ENAC-Robotique/fabs_motor_board/firmware/src/OdometryDiff.cpp

#include "OdometryDiff.h"
#include "math.h"
#include "encoders.h"

extern "C" {
#include "printf.h"
#include "globalVar.h"
#include "stdutil.h"
}
#include "utils.h"
#include "communication.h"
#include "BytesWriteBuffer.h"
#include "messages.h"

using namespace protoduck;


void OdometryDiff::set_pos(double x, double y, double theta) {
  _x = x;
  _y = y;
  _theta = theta;
}

void OdometryDiff::init() {
  initEnc1(true);
  initEnc2(false);
  initEnc3(false);
  initEnc4(true);

  auto cb_recalage = [this](Message& msg) {
      if(msg.has_pos() && msg.msg_type() == Message::MsgType::COMMAND) {
        double x = msg.pos().get_x();
        double y = msg.pos().get_y();
        double theta = msg.pos().get_theta();
        set_pos(x, y, theta);
    }
  };
  register_callback(cb_recalage);
}

void OdometryDiff::update_pos(double elapsed) {
    static systime_t lastOdomReportTime = 0;
    int32_t delta_left = get_delta_enc3();
    int32_t delta_right = get_delta_enc4();

    double length = ((double)(delta_left + delta_right)/2.0)/CODING_INC_PER_MM;
    double angle = ((double)(delta_right - delta_left)/CODING_INC_PER_MM)/CODING_WHEELBASE;

    speed = length / elapsed;
    omega = angle / elapsed;
    _x = _x + length*cos(_theta + angle/2.0);
    _y = _y + length*sin(_theta + angle/2.0);
    _theta = center_radians(_theta + angle);


    if(chVTTimeElapsedSinceX(lastOdomReportTime) > chTimeMS2I(PERIOD_ODOM_REPORT)) {
      sendOdomReport();
      lastOdomReportTime = chVTGetSystemTime();
    }
}

void OdometryDiff::update_mot(double elapsed) {
  static systime_t lastSlipReportTime = 0;
  int32_t delta_mot_left = get_delta_enc1();
  int32_t delta_mot_right = get_delta_enc2();

  speed_left  = static_cast<double>(delta_mot_left) / (MOTOR_INC_PER_MM*elapsed);
  speed_right = static_cast<double>(delta_mot_right)/ (MOTOR_INC_PER_MM*elapsed);

  double th_left = speed - omega * WHEELBASE / 2.0;
  double th_right = speed + omega * WHEELBASE / 2.0;
  double sl = th_left - speed_left;
  double sr = th_right - speed_right;
  double alpha = 0.1;
  slip_left  = (1-alpha) * slip_left  + alpha * sl;
  slip_right = (1-alpha) * slip_right + alpha * sr;

  if(chVTTimeElapsedSinceX(lastSlipReportTime) > chTimeMS2I(PERIOD_SLIP_REPORT)) {
    if(abs(slip_left) > SLIP_THRESHOLD || abs(slip_right) > SLIP_THRESHOLD) {
      Message msg;
      auto& slip_report = msg.mutable_slip();
      slip_report.set_slip_left(slip_left);
      slip_report.set_slip_right(slip_right);
      post_message(msg, Message::MsgType::STATUS, TIME_IMMEDIATE);
      lastSlipReportTime = chVTGetSystemTime();
    }
  }
}


msg_t OdometryDiff::sendOdomReport() {
  Message msg;
  auto& pos_report = msg.mutable_pos();
  pos_report.set_x(_x);
  pos_report.set_y(_y);
  pos_report.set_theta(_theta);
  msg_t ret = post_message(msg, Message::MsgType::STATUS, TIME_IMMEDIATE);

  if(ret != MSG_OK) {
    return ret;
  }


  auto& speed_report = msg.mutable_speed();
  speed_report.set_vx(speed);
  speed_report.set_vy(0);
  speed_report.set_vtheta(omega);
  ret = post_message(msg, Message::MsgType::STATUS, TIME_IMMEDIATE);
  return ret;
}
