ENAC-Robotique/fabs_motor_board/firmware/src/utils.cpp

#include "utils.h"
#include "BytesWriteBuffer.h"
#include "ch.h"
#include "communication.h"

using namespace protoduck;

/**
 * Centers an angle in radians to [-pi, pi[
 */
double center_radians(double angle){
  while (angle >= M_PI){
    angle -= 2 * M_PI;
  }
  while (angle < -M_PI){
    angle += 2 * M_PI;
  }
  return angle;
}


double clamp(double lo, double val, double hi) {
    if(val < lo) {return lo;}
    if(val > hi) {return hi;}
    return val;
}

msg_t post_message(Message& msg, Message::MsgType msg_type, sysinterval_t timeout) {
  BytesWriteBuffer* buffer;
  // get a free buffer
  msg_t ret = chMBFetchTimeout(&mb_free_msgs, (msg_t *)&buffer, timeout);
  if(ret != MSG_OK) {
    return ret;
  }

  msg.set_source(Message::Agent::DIFF);
  msg.set_msg_type(msg_type);
  msg.serialize(*buffer);
  // post the new message for the communication thread. no timeout.
  return chMBPostTimeout(&mb_filled_msgs, (msg_t)buffer, TIME_IMMEDIATE);
}
